WesleyNovaes-Dev/Serial_to_TCP_Industrial_Gateway_for_Weighing_Systems/Node_Test_Codes/Coleta foto.csv

Data | Hora | DadoBruto | IP_Conexao
02/10/2025 | 18:29:58 | I00.000 | 10.128.32.178
02/10/2025 | 18:29:59 | I00.000 I00.000 I00.000 I00.000 I00.000 I00.000 I00.000 I00.000 I00.000 I00.000 I00.000 I00.000 I00.000 I00.000 I00.000 I00.000 I00.000 I00.000 I00.000 | 10.128.32.178
02/10/2025 | 18:29:59 | E00.000 | 10.128.32.178
02/10/2025 | 18:29:59 | E00.000 E00.000 E00.000 E00.000 E00.000 E00.000 E00.000 E00.000 E00.000 E00.000 E00.000 E00.000 E00.000 E00.000 E00.000 E00.000 E00.000 E00.000 E00.000 | 10.128.32.178
02/10/2025 | 18:30:08 | I00.015 | 10.128.32.178
02/10/2025 | 18:30:08 | I00.015 I00.015 I00.015 I00.015 I00.015 I00.015 I00.015 I00.015 I00.015 I00.015 I00.015 I00.015 I00.015 I00.015 I00.015 I00.015 I00.015 I00.015 I00.015 | 10.128.32.178
02/10/2025 | 18:30:08 | I00.035 | 10.128.32.178
02/10/2025 | 18:30:08 | I00.035 I00.035 I00.035 I00.035 I00.035 I00.035 I00.035 I00.035 I00.035 I00.035 I00.035 I00.035 I00.035 I00.035 I00.035 I00.035 I00.035 I00.035 I00.035 | 10.128.32.178
02/10/2025 | 18:30:08 | I00.055 | 10.128.32.178
02/10/2025 | 18:30:08 | I00.055 I00.055 I00.055 I00.055 I00.055 I00.055 I00.055 I00.055 I00.055 I00.055 I00.055 I00.055 I00.055 I00.055 I00.055 I00.055 I00.055 I00.055 I00.055 | 10.128.32.178
02/10/2025 | 18:30:08 | I00.065 I00.065 I00.065 I00.065 I00.065 I00.065 I00.065 I00.065 I00.065 I00.065 I00.065 I00.065 I00.065 I00.065 | 10.128.32.178
02/10/2025 | 18:30:08 | I00.065 I00.065 I00.065 I00.065 I00.065 I00.065 | 10.128.32.178
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
02/10/2025 | 18:34:29 | E00.000 | 10.128.32.178
02/10/2025 | 18:34:29 | E00.000 E00.000 E00.000 E00.000 E00.000 E00.000 E00.000 E00.000 E00.000 E00.000 E00.000 E00.000 E00.000 E00.000 E00.000 E00.000 E00.000 E00.000 E00.000 | 10.128.32.178
